RobPo/PaperiNode/examples/08_KWhMonitor/progmem.h

/*
  HOTTI Weather Icons
*/

#ifndef PROGMEM_h
#define PROGMEM_h

// Icon CLEAR SKY
const unsigned char wIcon_01 [] PROGMEM= {
  0x00, 0x00, 0x00, 
  0x00, 0x18, 0x00, 
  0x00, 0x18, 0x00, 
  0x00, 0x00, 0x00, 
  0x0c, 0x3c, 0x30, 
  0x0c, 0xff, 0x30, 
  0x01, 0xff, 0x80, 
  0x03, 0xff, 0xc0, 
  0x07, 0xff, 0xe0, 
  0x07, 0xff, 0xe0, 
  0x07, 0xff, 0xe0, 
  0x6f, 0xff, 0xf6, 
  0x6f, 0xff, 0xf6, 
  0x07, 0xff, 0xe0, 
  0x07, 0xff, 0xe0, 
  0x07, 0xff, 0xe0, 
  0x03, 0xff, 0xc0, 
  0x01, 0xff, 0x80, 
  0x0c, 0xff, 0x30, 
  0x0c, 0x3c, 0x30, 
  0x00, 0x00, 0x00, 
  0x00, 0x18, 0x00, 
  0x00, 0x18, 0x00, 
  0x00, 0x00, 0x00, 
};


// Icon FEW CLOUDS
const unsigned char wIcon_02 [] PROGMEM= {
  0x00, 0x00, 0x00, 
  0x00, 0x00, 0xf0, 
  0x01, 0xe3, 0xfc, 
  0x03, 0xfb, 0xfc, 
  0x07, 0xf9, 0xfe, 
  0x07, 0xfc, 0x3e, 
  0x07, 0xff, 0xde, 
  0x0f, 0xff, 0xdc, 
  0x3f, 0xff, 0xec, 
  0x7f, 0xff, 0xf0, 
  0xff, 0xff, 0xf8, 
  0xff, 0xff, 0xfc, 
  0xff, 0xff, 0xfc, 
  0x7f, 0xff, 0xfc, 
  0x7f, 0xff, 0xf8, 
  0x1e, 0xfb, 0xf0, 
  0x00, 0x00, 0x00, 
  0x00, 0x00, 0x00, 
  0x00, 0x00, 0x00, 
  0x00, 0x00, 0x00, 
  0x00, 0x00, 0x00, 
  0x00, 0x00, 0x00, 
  0x00, 0x00, 0x00, 
  0x00, 0x00, 0x00, 
};


// Icon SCATTERED CLOUDS
const unsigned char wIcon_03 [] PROGMEM= {
  0x00, 0x00, 0x00, 
  0x00, 0x00, 0x00, 
  0x01, 0xe0, 0x00, 
  0x03, 0xf8, 0x00, 
  0x07, 0xf8, 0x00, 
  0x07, 0xfc, 0x00, 
  0x07, 0xff, 0xc0, 
  0x0f, 0xff, 0xc0, 
  0x3f, 0xff, 0xe0, 
  0x7f, 0xff, 0xf0, 
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
  0x00, 0x00, 0x00, 
  0x0b, 0xff, 0xe8, 
  0x00, 0x00, 0x00, 
  0x00, 0x00, 0x00, 
  0x01, 0x7f, 0x40, 
  0x00, 0x00, 0x00, 
  0x00, 0x00, 0x00, 
  0x00, 0x00, 0x00, 
  0x00, 0x00, 0x00, 
  0x00, 0x00, 0x00, 
};

// DUMMY for PGM2FLASH
const byte pic [] PROGMEM= {  0x00 };

#endif
