RobPo/PaperiNode/examples/08_KWhMonitor/DS2401.cpp

/******************************************************************************************
* Copyright 2017 Ideetron B.V.
*
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
* You should have received a copy of the GNU Lesser General Public License
* along with this program.  If not, see <http://www.gnu.org/licenses/>.
******************************************************************************************/
/****************************************************************************************
* File:     DS2401.cpp
* Author:   Gerben den Hartog
* Company:	Ideetron B.V.
* Website:  http://www.ideetron.nl/LoRa
* E-mail:   info@ideetron.nl
* Created on:         13-01-2017
* Supported Hardware: ID150119-02 Nexus board with RFM95
****************************************************************************************/
#include <stdint.h>
#include "Arduino.h"
#include "DS2401.h"
#include "paperinode.h"

/*
*****************************************************************************************
* Description:  Function is used to read the all the bytes provide by the DS2401
*
* Arguments:    *DS_Bytes pointer to an array of 8 uint8_ts
*****************************************************************************************
*/
bool DS_Read(uint8_t *DS_Bytes)
{
	uint8_t i;

	//Preform reset pulse
	pinMode(DS2401,OUTPUT);
	digitalWrite(DS2401,LOW);
	delayMicroseconds(700);
	pinMode(DS2401,INPUT);
	delayMicroseconds(700);

	//Send command 0x33 LSB
	DS_WR1();
	DS_WR1();
	DS_WR0();
	DS_WR0();
	DS_WR1();
	DS_WR1();
	DS_WR0();
	DS_WR0();

	//Read DS bytes
	for (i = 0 ; i < RAM_SIZE ; i++)
	{
		DS_Bytes[i] = DS_ReadByte();
	}

	//Shutdown DS2401
	digitalWrite(DS2401, HIGH);  
	
	// Check whether the CRC matches with the last byte from the DS2401.
	return DS_CheckCRC(DS_Bytes);
}

/*
*****************************************************************************************
* Description:  Function is used to write a logical 1 to the DS2401
*****************************************************************************************
*/
void DS_WR1(void)
{
	pinMode(DS2401,OUTPUT);
	digitalWrite(DS2401,LOW);
	delayMicroseconds(2);
	pinMode(DS2401,INPUT);
	delayMicroseconds(80);
}

/*
*****************************************************************************************
* Description:  Function is used to write a logical 0 to the DS2401
*****************************************************************************************
*/
void DS_WR0(void)
{
	pinMode(DS2401,OUTPUT);
	digitalWrite(DS2401,LOW);
	delayMicroseconds(80);
	pinMode(DS2401,INPUT);
	delayMicroseconds(2);
}

/*
*****************************************************************************************
* Description:  Function is used to read the one byte provided by the DS2401
*
* Return:       Returns the byte received from the DS2401
*****************************************************************************************
*/
uint8_t DS_ReadByte(void)
{
	uint8_t DS_Byte = 0;
	uint8_t i, t = 1;

	for (i = 0 ; i < 8 ; i++)
	{
		pinMode(DS2401,OUTPUT);
		digitalWrite(DS2401,LOW);
		delayMicroseconds(2);
		pinMode(DS2401,INPUT);
		delayMicroseconds(10);
		
		if(digitalRead(DS2401) == 1)
		{
		  DS_Byte |= t;
		}

		t = t << 1;
		delayMicroseconds(80);
	}
	return DS_Byte;
}

/*
*****************************************************************************************
* Description	: This function does a CRC check on the received data from the DS2401
* Arguments		: *DS_bytes pointer to the arry that holds the DS bytes
* Return		: Returns 0x01 when CRC check is OK
*****************************************************************************************
*/
bool DS_CheckCRC(uint8_t *DS_bytes)
{
	uint8_t DS_current_byte = 0x00;
	uint8_t DS_crc          = 0x00;
	uint8_t DS_Polynom      = 0x0C;
	uint8_t DS_crc_carry    = 0x00;
	uint8_t i               = 0x00;
	uint8_t j               = 0x00;

	/*Loop for all 6 DS bytes*/
	for (i = 0 ; i < 7 ; i++)
	{
		DS_current_byte = DS_bytes[i]; //Get first byte

		/*Calculate CRC for all bits*/
		for (j = 0 ; j < 8 ; j++)
		{
			/*XOR bit 0 with bit 0 of current CRC*/
			if ((DS_crc & 0x01) != (DS_current_byte & 0x01))
			{
				DS_crc_carry = 0x80;
			}
			else
			{
				DS_crc_carry = 0x00;
			}

			/*shift CRC*/
			DS_crc = DS_crc >> 1;

			/*Check for carry*/
			if (DS_crc_carry == 0x80)
			{
				DS_crc = DS_crc | DS_crc_carry;
				DS_crc = DS_crc ^ DS_Polynom;
			}

			DS_current_byte = DS_current_byte >> 1;
		}
	}

	// Check whether the calculated CRC and the last received byte match. When they do retrun true to indicate that the received bytes are valid otherwise return false
	if (DS_crc == DS_bytes[7])
	{
		return true;
	}
	return false;
}
